foresail/fs1_psd_sun_sensor/simulations/tia.asc

C1: cap; 470n
C2: cap; 200p
C3: cap; 30p
I1: current; PWL file=current_input.txt; AC 100u
R1: res; 9.1k
R2: res; 1G
U1: opamp2; LMV342
V1: voltage; 3.3
V2: voltage; 1.8
Named nets: 0, OUT, IN, Vref, VCC
;ac oct 10 100m 100
.lib LMV342.cir
Terminal
capacitance
Photodiode
.tran 5
